JohnnyElectronic/EMF_Meters/10_LED_EMF_Meter_Replica/r1/img/10_LED_Lights2.jpg

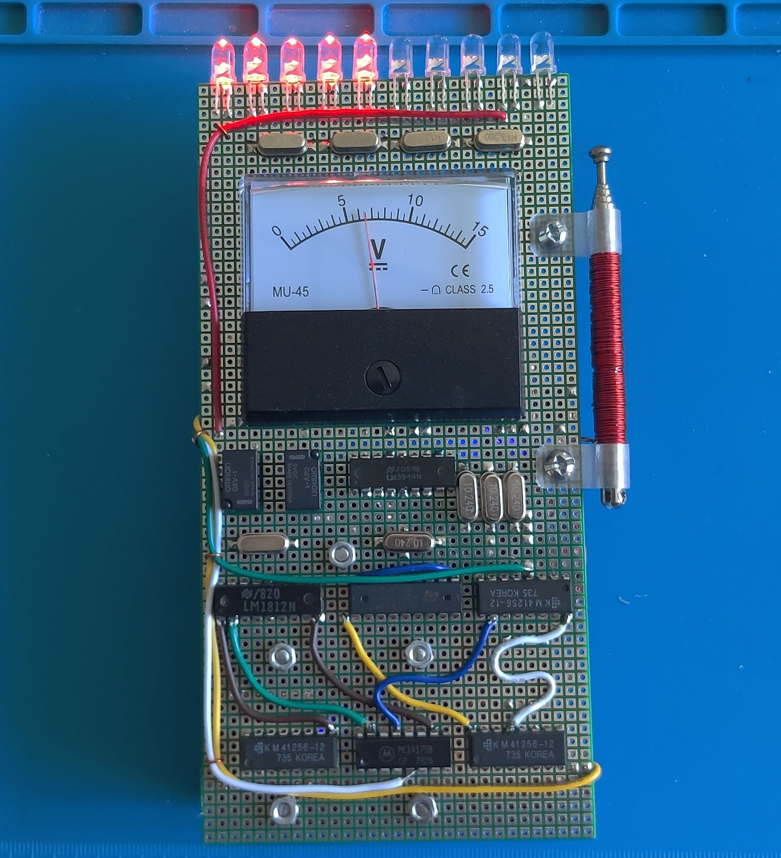
10_LED_EMF_Meter_Replica/r1/img/10_LED_Lights2.jpg
