JohnnyElectronic/EMF_Meters/EMF_Meter_Replica/r1/img/EMF_Meter_9v_buck_converted_b.jpg

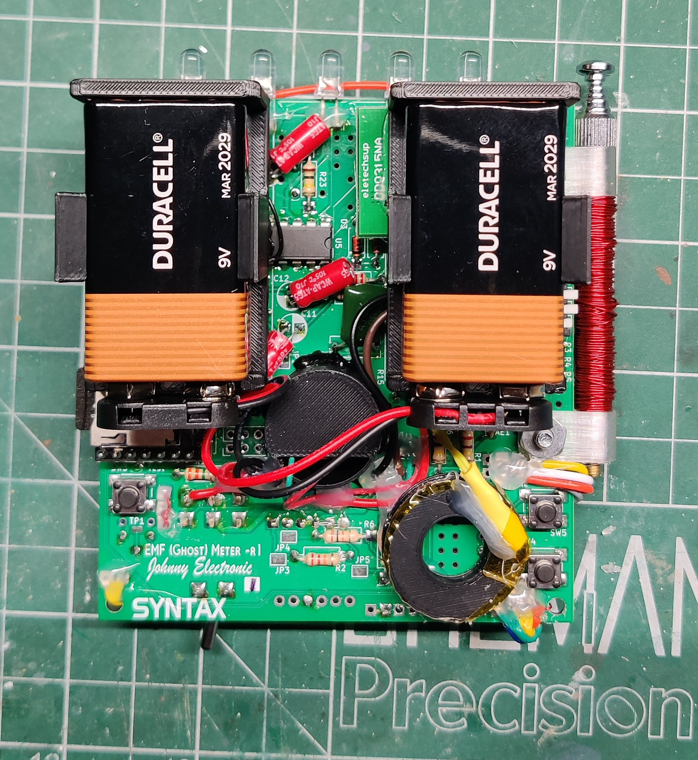
EMF_Meter_Replica/r1/img/EMF_Meter_9v_buck_converted_b.jpg
