JohnnyElectronic/EMF_Meters/EMF_Meter_Replica/r1/img/EMF_Meter_Label_0113_28x3.png

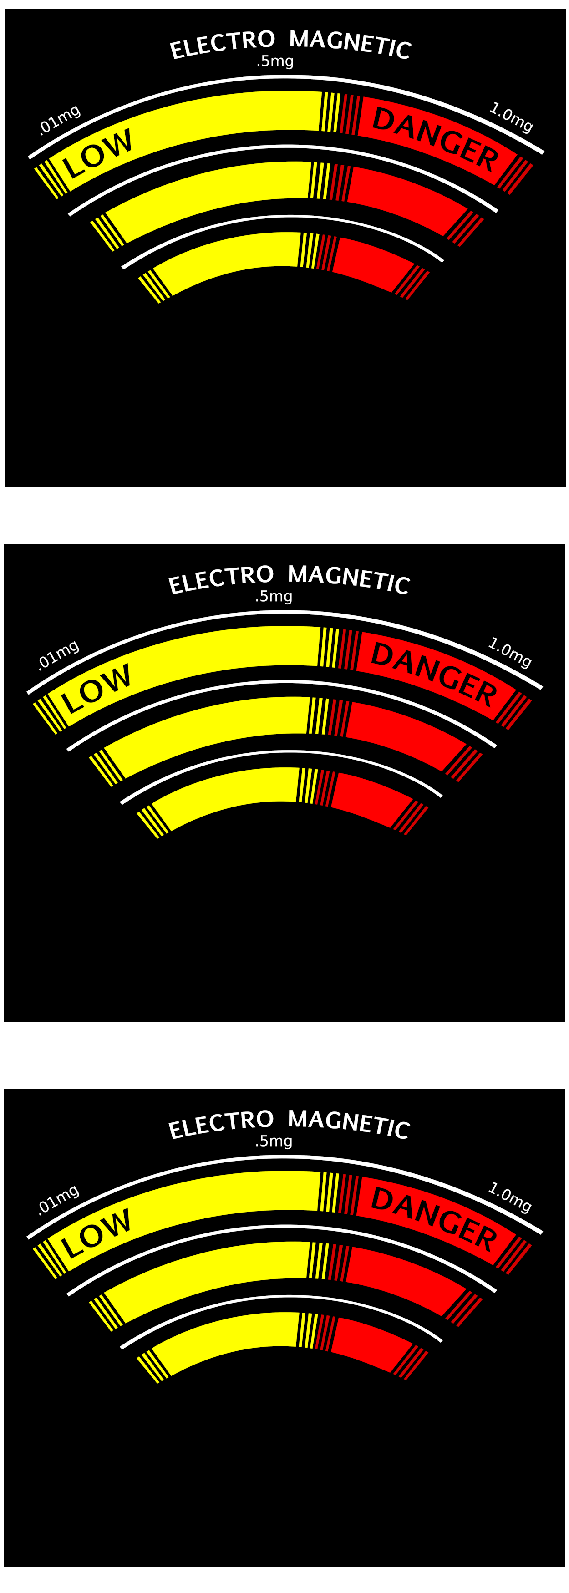
EMF_Meter_Replica/r1/img/EMF_Meter_Label_0113_28x3.png
