JohnnyElectronic/EMF_Meters/EMF_Meter_Replica/r2/img/EMF_6v_back.jpg

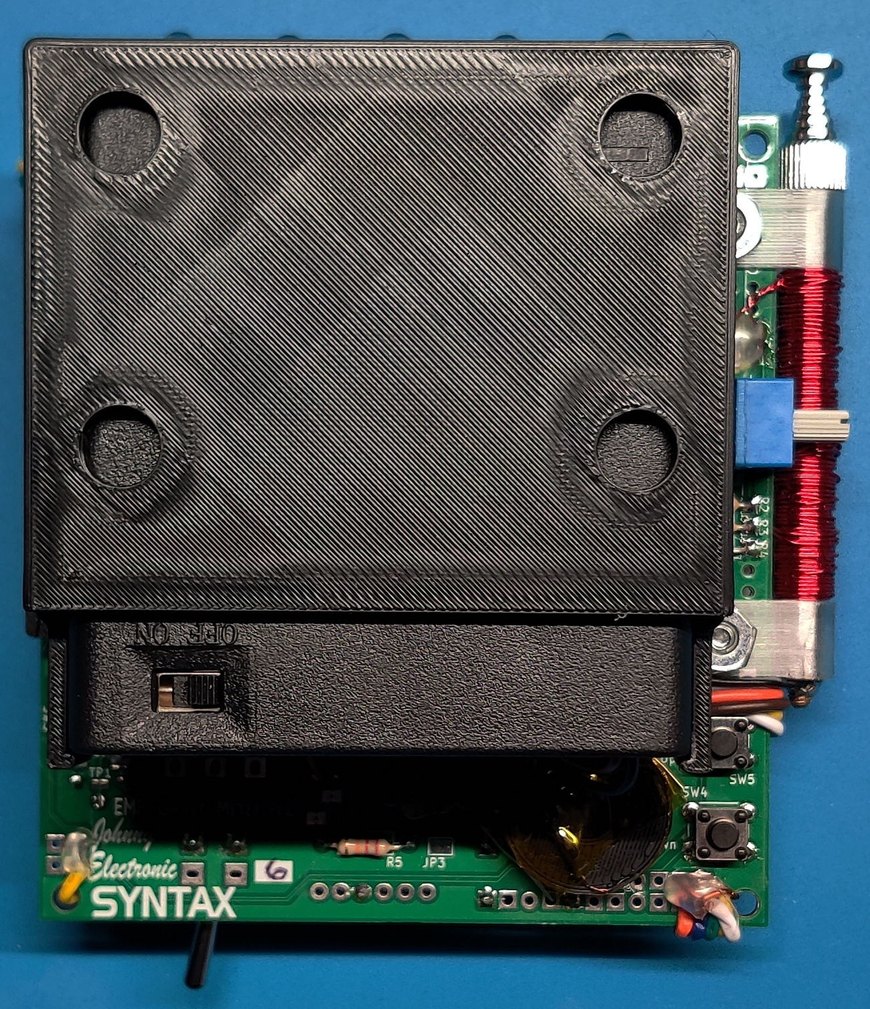
EMF_Meter_Replica/r2/img/EMF_6v_back.jpg
