JohnnyElectronic/EMF_Meters/EMF_Meter_Replica/r2/img/EMF_9v_front.jpg

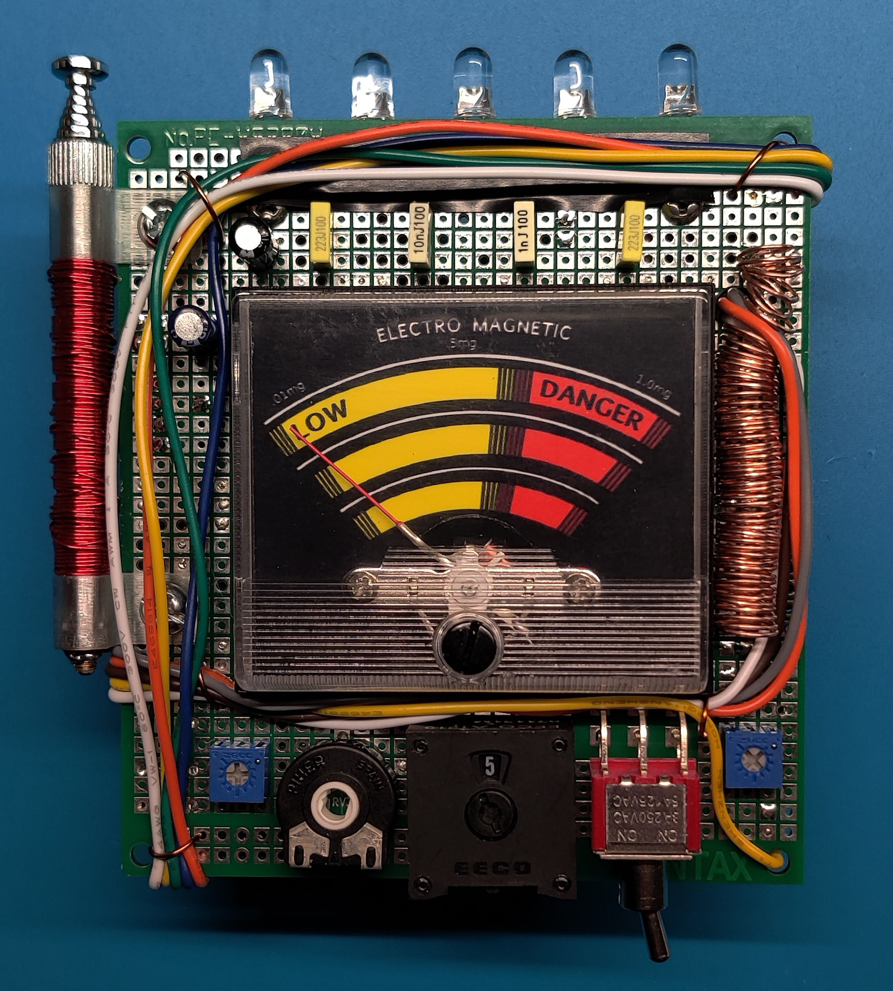
EMF_Meter_Replica/r2/img/EMF_9v_front.jpg
