JohnnyElectronic/EMF_Meters/10_LED_EMF_Meter_Replica/r2/doc/Top_Layout_Guide.pdf

t,6g*'

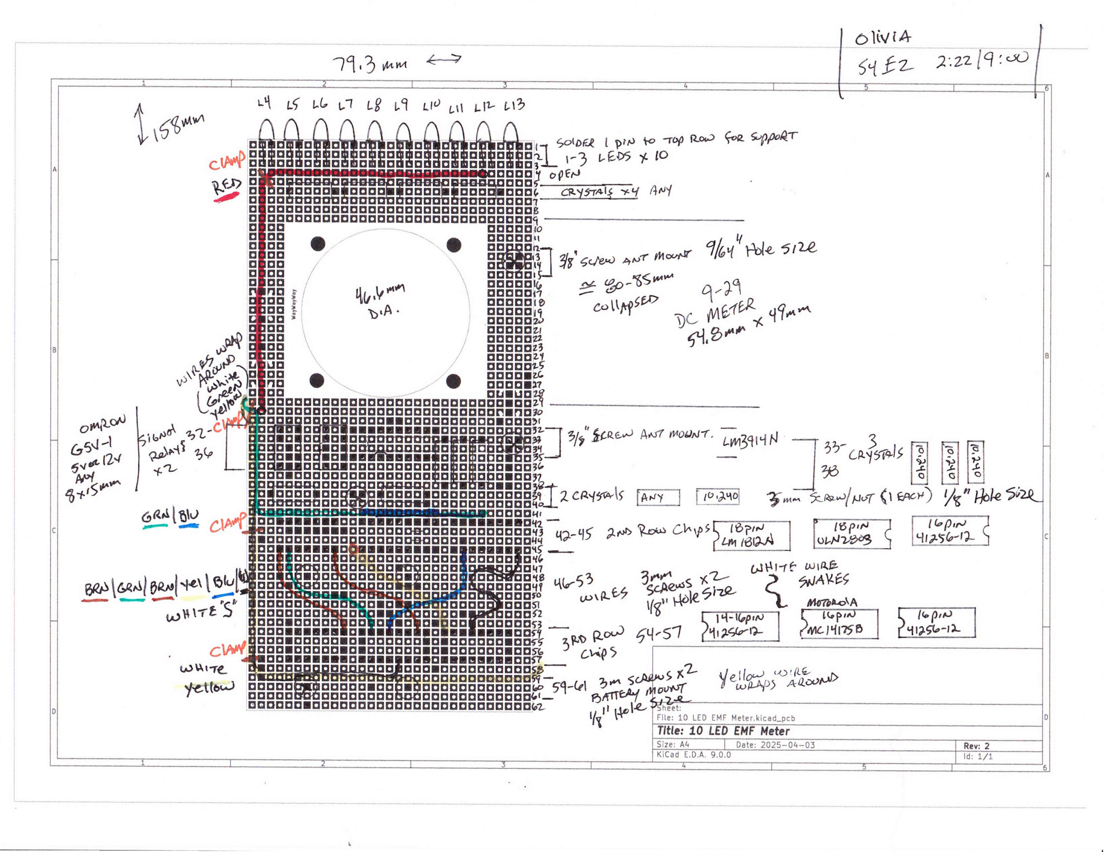
[picture p124: page 1]

'11,1 u- <'--' | ol(vl4 51tL 2"zz lq t'a

6aI[6tur .---

r"1 1ld ;rl LIL LtV
n QTDFJ I prp {. '-l t Lr>s | Qz opP"er lo 1oP fLa,2 )c lo o(Jl > | o0eP '-ffi*Vt | Apl

1r' s./* atn rhsqs ila"lt' r\>le 5 rLL

40.v"
b'A '

9t- to,g-XSVe
- oir1,1t* a']1 \L iua@*ql^^

4,bnn
"t't

or&d
?:::;r
fiTl*-

ll1ificto,,

A^r7 L'ouNa. tt5lrltl 150- ro?rds g )% | El' Tcag*ls tA^,y I t@ g^7**-w"rlp"r (ttxv) IEt Ifl L9 L9 ,/r, Lht"

6oAt*u]oj"l*'tB
purre

.9

cwrl,

,a-ts e,D?'bt 2n'rW,a61 ;W1 Vi-W,{l,

rrur7e

yatto'*) | ""# '1"1fr,f,!f*,,

5neetr
Fite:10 LED EMF Meter.kicad_pcb

te:2025-04-03

"rw
F*"; l"-
',l,,te'l t*:ii,*'* "I'x'itt" ' | L xasTutA ww*lw L\v5, 31fr*s ft'^ 'ff:'*w* -lpo eo., 5q'51 J | -.'^ | < | I cnp5
