JohnnyElectronic/EMF_Meters/10_LED_EMF_Meter_Replica/r1/doc/10_LED_EMF_Meter_Build_r1.1.pdf

# 10 LED EMF Meter Build

## Contents

## Description

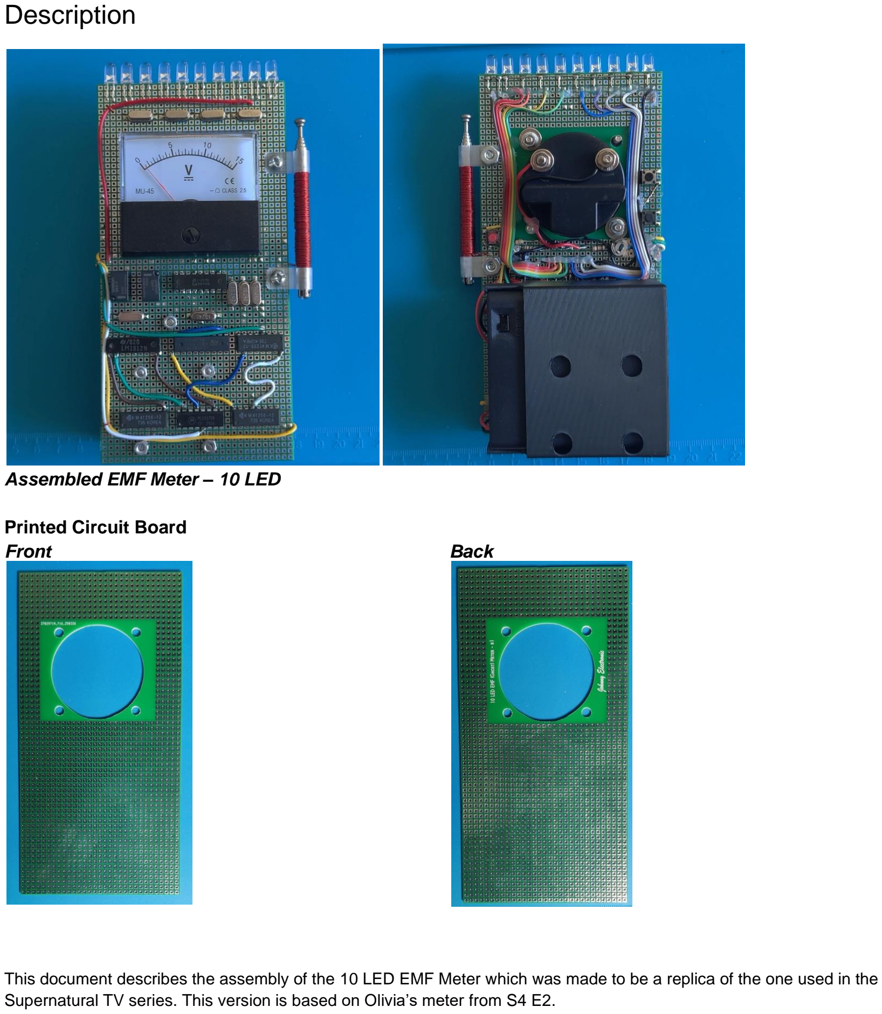
[picture p131: page 2]

Assembled EMF Meter – 10 LED

Printed Circuit Board
Front | Back

This document describes the assembly of the 10 LED EMF Meter which was made to be a replica of the one used in the Supernatural TV series. This version is based on Olivia’s meter from S4 E2.

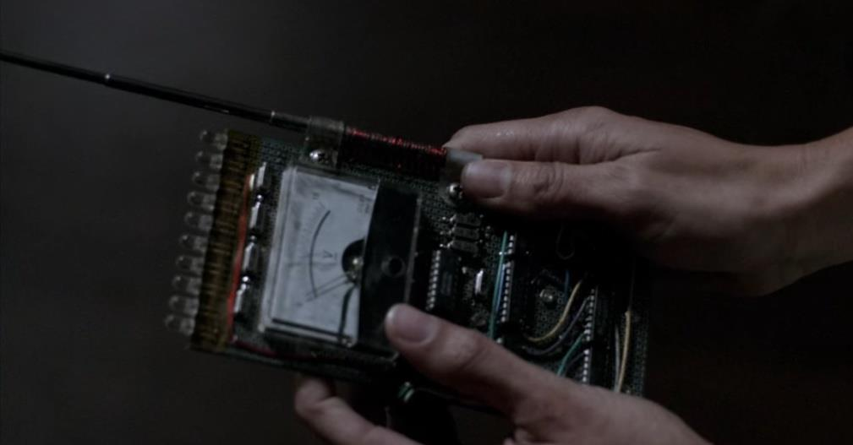
[picture p132: figure]

Olivia’s EMF Meter (S4 E2 2:22)

This is a prop only EMF meter and can manually create EMF events by pressing the program button or run a selection of pre-programmed sequences.

## Board Details

- PCB Dimensions: 79 mm x 158 mm
- 4 AA batteries to provide 6v with power
- Meter is a DC 0-15
- 10 LEDS in BAR mode
- 9 non-functional crystals
- LM3914 IC – functional
- 6 random IC’s, non-functional
- Right side mounted antenna, cosmetic
- 2 low voltage signal relays, non-functional

### Parts List

See the 10 LED EMF Board BOM for a detailed list of parts and part suppliers. A link to Github is provided in the references section at the end of this document.

## Pre-Assembled Boards

This board is currently hand built on perfboard using point to point solder connections. Thus pre-assembled boards will be very limited.

## Assembly Guide

Caution: Electrostatic discharge (ESD) is a sudden and momentary flow of electric current between two differently-charged objects when brought close together or when the dielectric between them breaks down, often creating a visible spark associated with the static electricity between the objects. ¹

1 Definition provided by From Wikipedia, the free encyclopedia. For more information on ESD see https://en.wikipedia.org/wiki/Electrostatic_discharge

This type of shock can cause damage to ESD sensitive parts such as those used in this build. Proper ESD protection and soldering equipment should be used to prevent damage to parts during assembly and implementation into your project.

Assembly Planning

This assembly uses all through hole parts except for possibly the 5-volt regulator. A medium to fine tip soldering iron is useful along with 0.034” or smaller flux core solder and extra flux if needed. See the references section for a YouTube video link on assembling this board.

### PCB Assembly

- PCB assembly can be completed in any order.
- This is a perfboard assembly and you will need to use the schematic for all the point to point connections. I’ve included a copy of my layout guide for functional and non-functional part placements.
- There is also an image of the board assembly with the battery pack removed so you can see a suggested layout.
- Since the battery supply is only 6v a LDO 5-volt regulator of at least 500ma will be needed to power the ATTiny85 and DFPlayer module.
- The position of the ATTiny85 should allow it to be removed easily for reprogramming. Suggest a socket be used.
- The position of the DFPlayer should allow easy access to the SD card. Also, the speaker will need to connect to this part and attach to the back of the battery holder or a different location.
- Hot glue any wire connections for added support.

### Antenna, Coil Assembly and Mounting

A coil of wire is wrapped around a telescopic antenna. I used 26 AWG red enameled wire to wrap around the antenna. Before wrapping the antenna with wire, you will want to attach the p-clips with 6-32 3/8” screws with nuts. You will need to drill holes into the PCB for the antenna to be mounted. Then align the P-clips to the hole positions but do not mount it to the board. Once you have the p-clips aligned tighten the nuts so the clips do not move. You can now start wrapping the enameled wire between the two p-clips. You can start/end the wrap from either end.
- Make the first layer wrap tight and uniform around the antenna. On the second pass feel free to add multiple layers and give it a non-uniform look much like a free-handed wire wrap.
- Mount the antenna/coil using P-Clips. 3D files are also available for printing these.
- You can solder the wire ends to one of the perfboard pads to make it look functional.

### Attach Speaker

- Connect the speaker to pins 6 & 8 of the DFPlayer module. I suggest the speaker be hot glued to the back of the battery pack holder but you may see other options.

### Mounting Battery Pack

- Use the AA battery pack holder as a drilling template to drill 4 holes into the PCB for mounting. Look at the reference layout for proper positioning.
- Using hot glue attach the speaker to the bottom of the battery pack holder. Make sure you have enough wire to allow the battery pack to attach to the PCB.
- Use either 4-40 or M3 screws to mount the battery pack holder with a minimum of 8-10mm standoffs. I’ve provided some 3D files a 4-AA battery pack holder so they can be mounted to this board.

### Mounting Meter

- The DC meter is mounted in the cutouts/holes provided in the PCB.
- Connect the meter wires noting the proper polarity.

### Adding Cosmetic Wires

- The available images for this meter are limited. I’ve made some guesses as to wiring for the meter front. All wires are non-functional except for the top red wire so placement is at the builder’s discretion. The top RED wire was used to provide LED + power. See “Assembly Images” for suggested wire routes.

## Sound Files (MP3)

The sound files are stored in a folder named /mp3 on the SD card. Six files are available but only five are used in the program for the EMF meter. This table lists the files, functionality, and associated code define. The sound files are available in Github (The same files are used for the EMF Meter Build and they are available from that folder under /mp3). The link is in the references section at the end of this document.

File Name | Define Name | Function
0001_emf start.mp3 | EMF_TONE_START | Initial start up when a signal is detected or test button pressed
0002_emf low short.mp3 | EMF_TONE_LOW | Used for mid-point signals that are neither high or low
0003_emf steady short.mp3 | EMF_TONE_STEADY | Not used
0004_emf steady long.mp3 | EMF_TONE_STEADYL | High tone when signal reaches maximum
0005_emf steady end.mp3 | EMF_TONE_END | Signal going back down to off
0006_emf power up.mp3 | EMF_POWER_UP | Used for initial setup/power on.

## EMF Meter Adjustments and Power Up

1. Before powering up the meter check for any shorts by doing an ohm measurement across the +/-battery connector.
2. Adjust the meter potentiometer to the midpoint.
3. Insert SD card with audio files in to the DFPlayer.
4. Install the AA batteries and flip the power pack switch on.
5. With in a second you should see the meter briefly deflect and a sound from the DFPlayer.
6. Press and hold the Test/Program Button and you should see the LEDS and VU Meter deflect and some sound effects. While keeping the button pressed adjust the meter potentiometer until all 10 LEDS are on.
7. Using a long button press you can manually make EMF events.
8. A quick button press will cycle through the pre-programmed EMF event sequences. An LED will light when a programmed sequence is running.
9. While pressing the Test/Program button check that the Volume Up/Down buttons are functional.
10. Removing the AA battery pack from the holder is easiest by gently pulling the locking tabs away from the battery pack and shaking the meter a few times to let gravity release the battery back. You should now be able to slide the pack out completely.

## Assembly Images

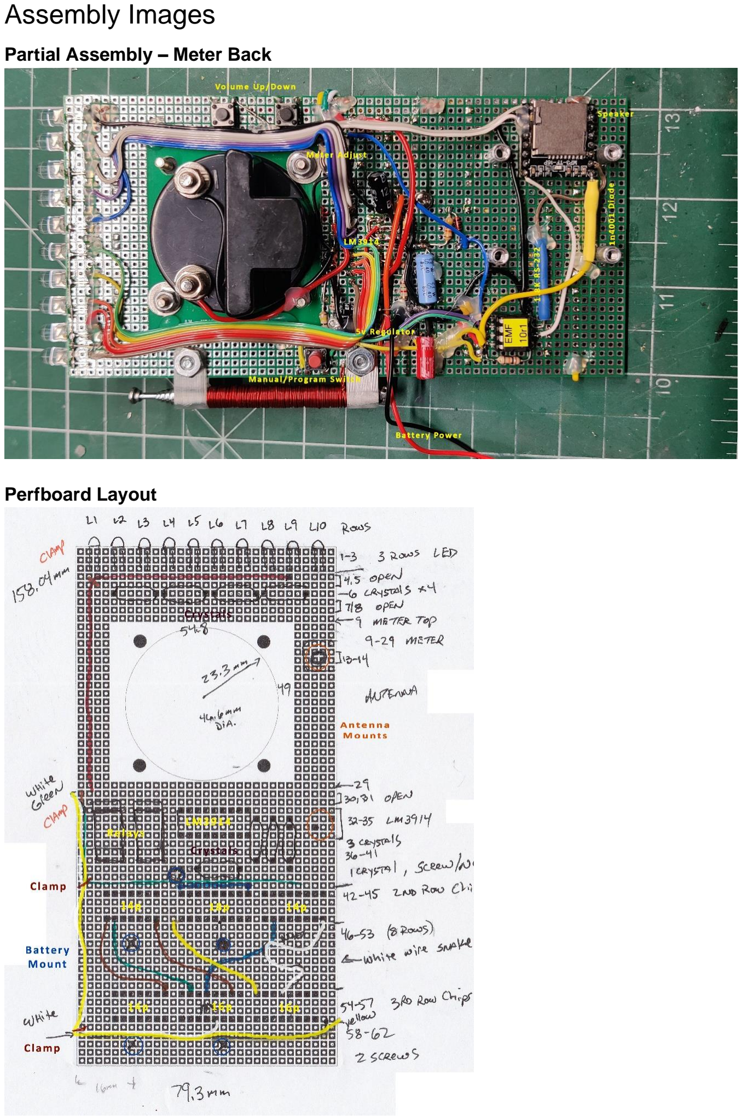
[picture p133: page 6]

Partial Assembly – Meter Back

Perfboard Layout

## References

- Github: Development board documentation, schematics, and related files.
- https://github.com/JohnnyElectronic/EMF_Meters/
- YouTube: Board assembly and project videos that are related to this project.
- https://www.youtube.com/@Johnny_Electronic

## Revisions

R1.1 First board release, First document release

Disclaimer

This information is provided “as-is” with no representation or warranty of any kind whether express or implied. However, I’ve tried to make this document (as well as the supporting videos) as useful and accurate as possible. If you find something that is incorrect or confusing, please let me know as I would like to make the correction so others will not have the same issue.

This meter is for entertainment purposes only and there is no representation as to the accuracy of the meter readings.

Feel free to email me any time for issues you may have with this build.
johnnyelectronic1@gmail.com

Legal note

Microchip, AVR, tinyAVR, megaAVR, ICSP, In-Circuit Serial Programming, are names of Microchip, it’s products and product lines, and as such are all trademarks of Microchip.
