JohnnyElectronic/EMF_Meters/EMF_Meter_Replica/r1/img/Partial_Assembly2.jpg

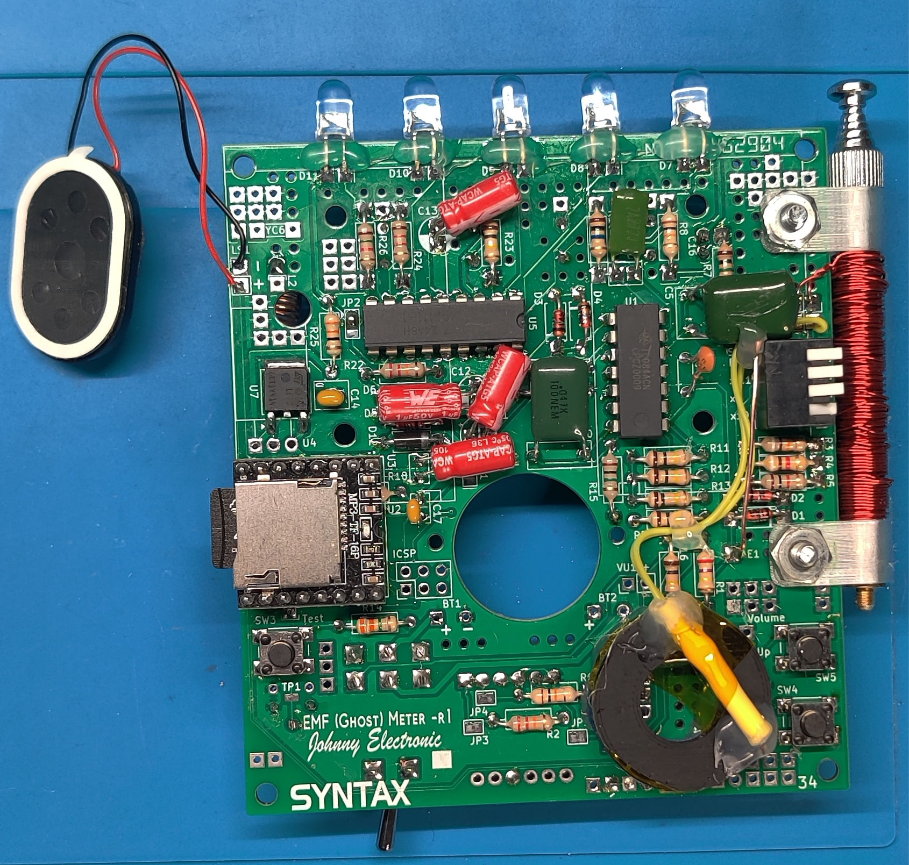
EMF_Meter_Replica/r1/img/Partial_Assembly2.jpg
