JohnnyElectronic/EMF_Meters/EMF_Meter_Replica/Journal/EMF Meter Journal Page_br_tn.jpg

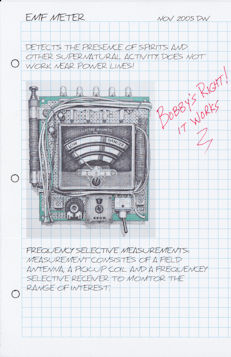
EMF_Meter_Replica/Journal/EMF Meter Journal Page_br_tn.jpg
