JohnnyElectronic/EMF_Meters/EMF_Meter_Replica/Journal/EMF Meter Journal Page_left_cs_tn.jpg

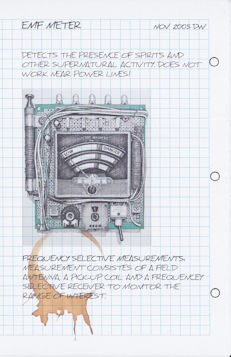
EMF_Meter_Replica/Journal/EMF Meter Journal Page_left_cs_tn.jpg
