JohnnyElectronic/EMF_Meters/EMF_Meter_Replica/r2/schematics/EMF_Meter_r2.pdf

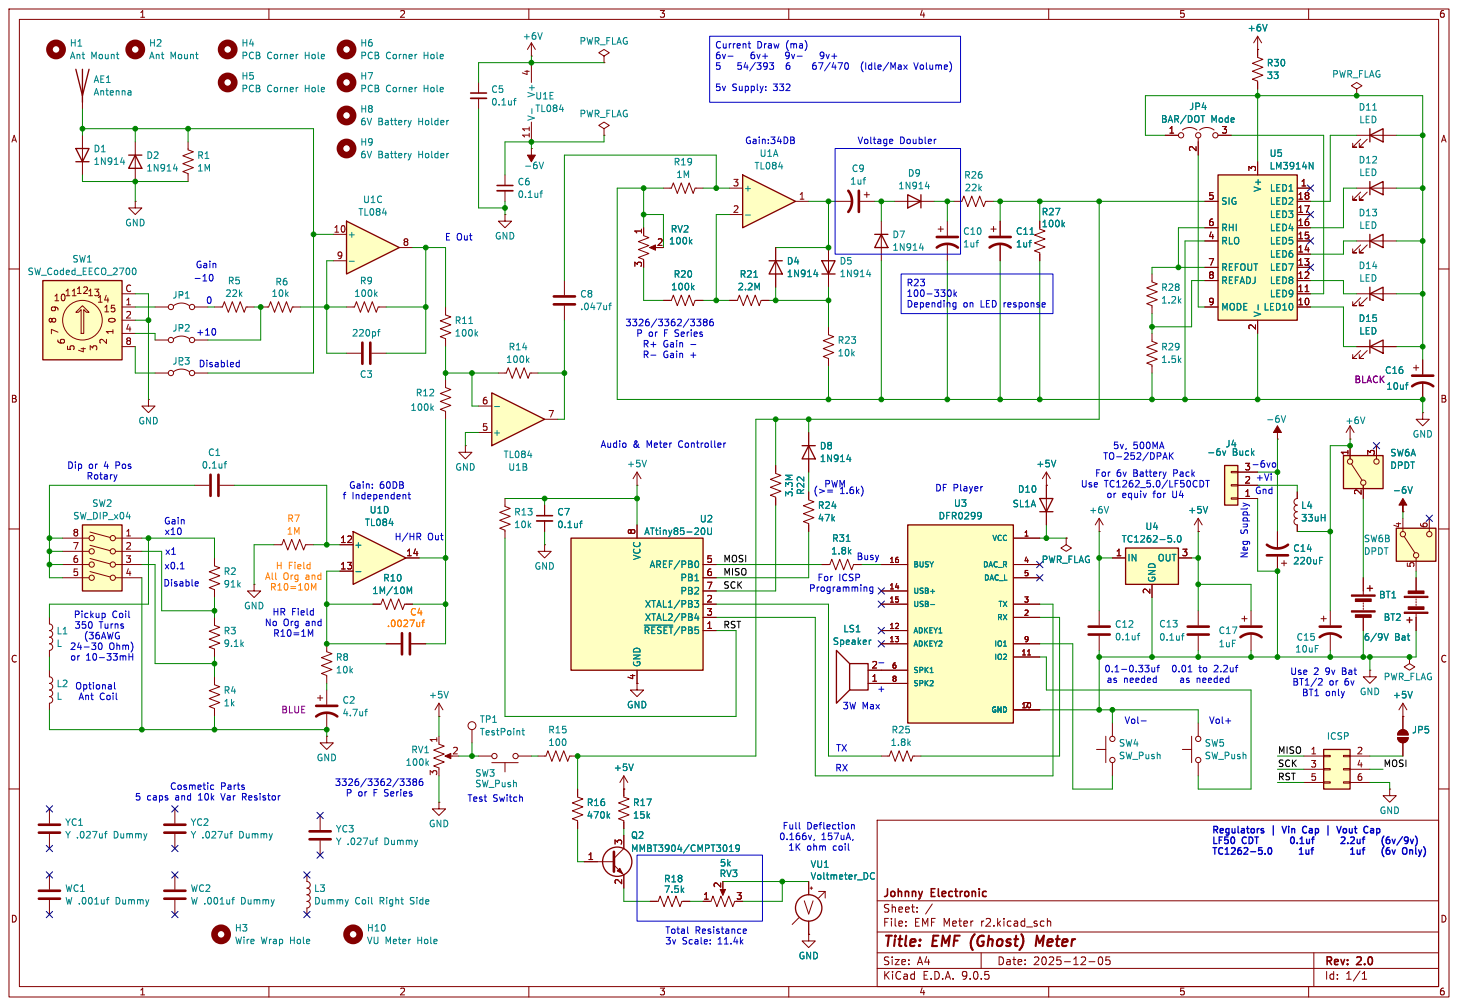
[picture p160: page 1]

6V Battery Holder H6PCB Corner Hole R11

JP1~ YC2 Y .027uf Dummy WC2 W .001uf Dummy H3 Wire Wrap Hole

3326/3362/3386 P or F Series R+ Gain - R- Gain +

TO-252/DPAK HR Field No Org and R10=1M

or equiv for U4 H Field All Org and R10=10M
