JohnnyElectronic/EMF_Meters/10_LED_EMF_Meter_Replica/r2/schematics/10_LED_EMF_Meter_r2.pdf

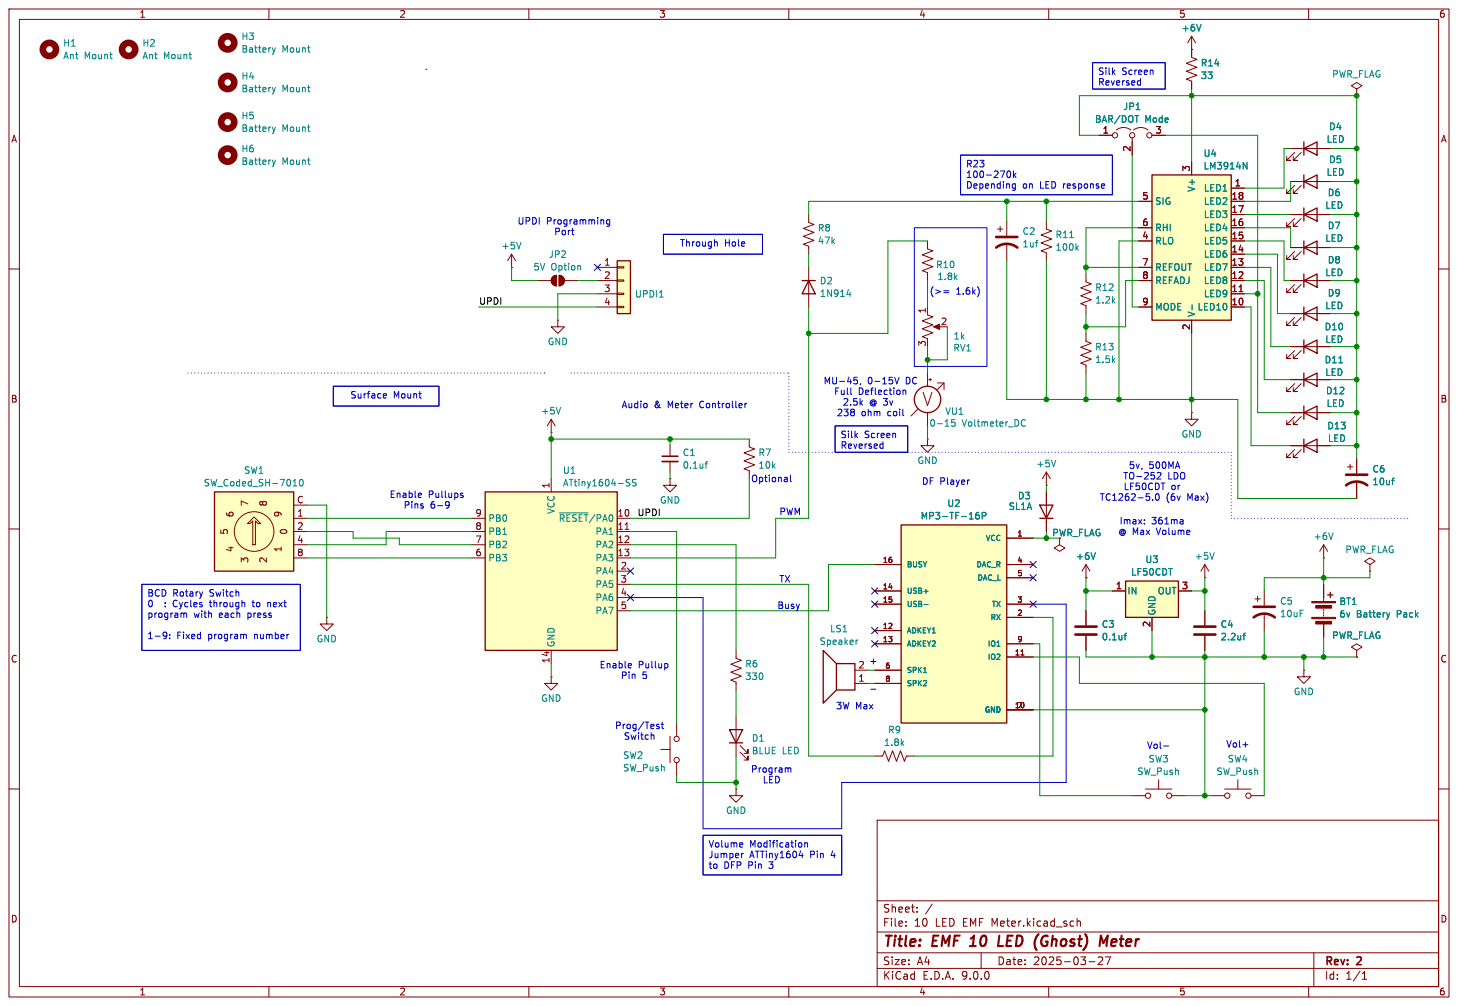
[picture p161: page 1]

LED GND
2.5k @ 3v 238 ohm coil 3W Max Busy

100-270k Depending on LED response

Imax: 361ma @ Max Volume Prog/Test Switch
