JohnnyElectronic/EMF_Meters/EMF_Meter_Replica/r1/schematics/EMF_Meter_r1.1.pdf

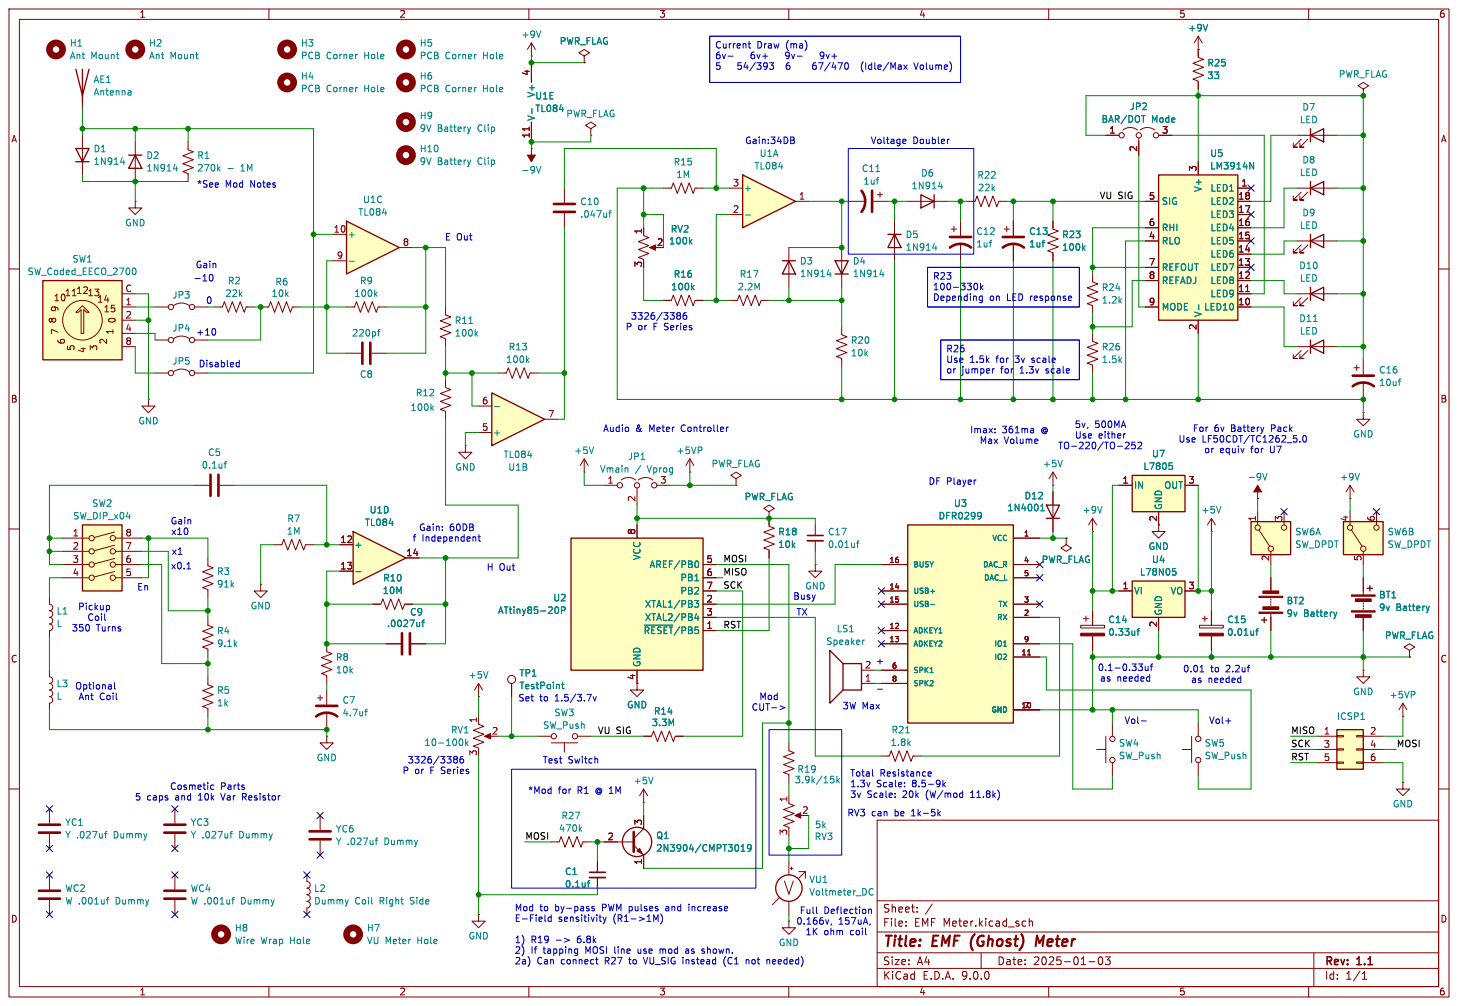
[picture p162: page 1]

H4PCB Corner Hole H3PCB Corner Hole +
9V Battery Clip H10

9V Battery Clip H5PCB Corner Hole H6PCB Corner Hole

or jumper for 1.3v scale R23

5v, 500MA Use either TO-220/TO-252

YC6 Y .027uf Dummy L2Dummy Coil Right Side GND
