JohnnyElectronic/EMF_Meters/10_LED_EMF_Meter_Replica/r1/schematics/10_LED_EMF_Meter.pdf

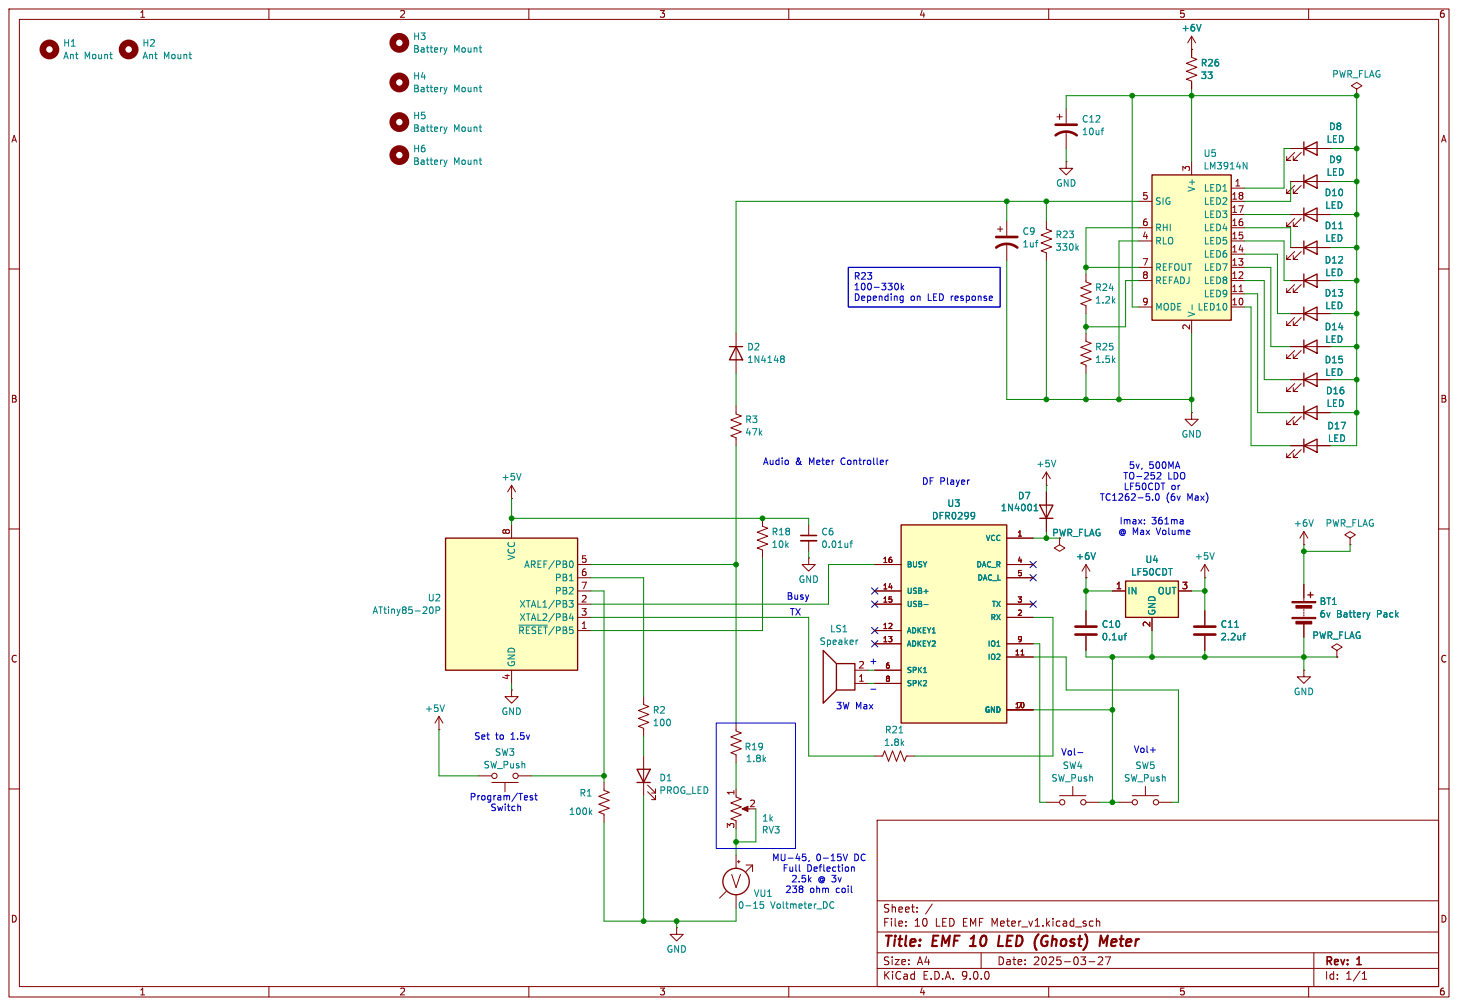
[picture p163: page 1]

100-330k Depending on LED response
