JohnnyElectronic/EMF_Meters/EMF_Meter_Replica/3D/EMF_Meter_Base_r2.pdf

2

1

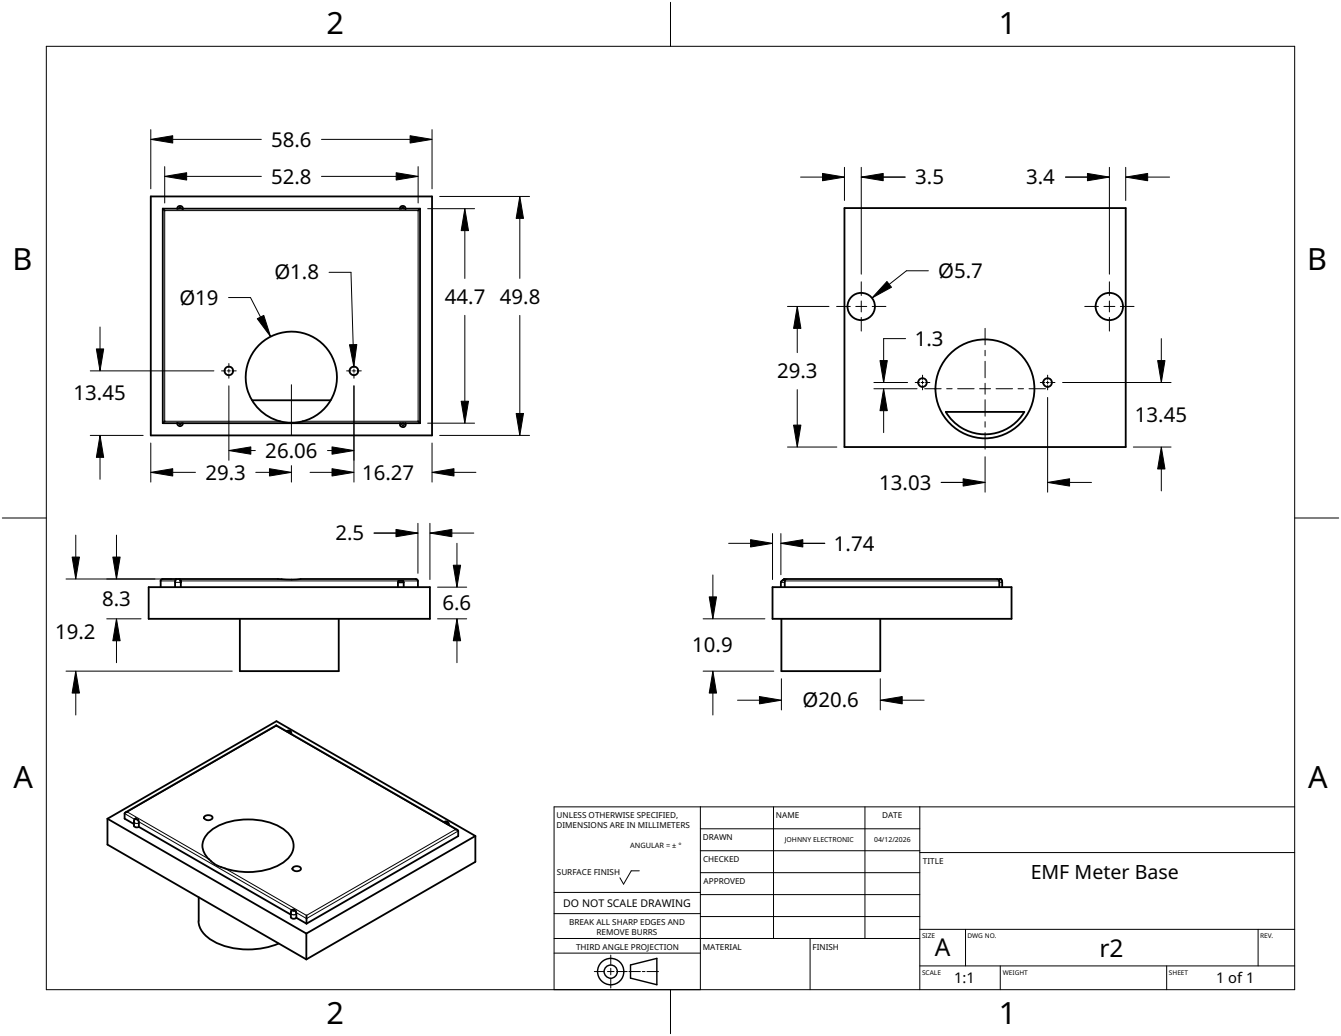
[picture p164: page 1]
MATERIAL; FINISH

UNLESS OTHERWISE SPECIFIED, DIMENSIONS ARE IN MILLIMETERS ANGULAR = ± ° SURFACE FINISH | | NAME | DATE

DRAWN | JOHNNY ELECTRONIC | 04/12/2026

CHECKED | | | TITLE EMF Meter Base

APPROVED

DO NOT SCALE DRAWING
BREAK ALL SHARP EDGES AND
REMOVE BURRS
THIRD ANGLE PROJECTION

SIZE A | DWG NO. r2 | REV.

SCALE 1:1 | WEIGHT | SHEET 1 of 1
