JohnnyElectronic/EMF_Meters/EMF_Meter_Replica/3D/9v_Battery_Holder.pdf

2
1

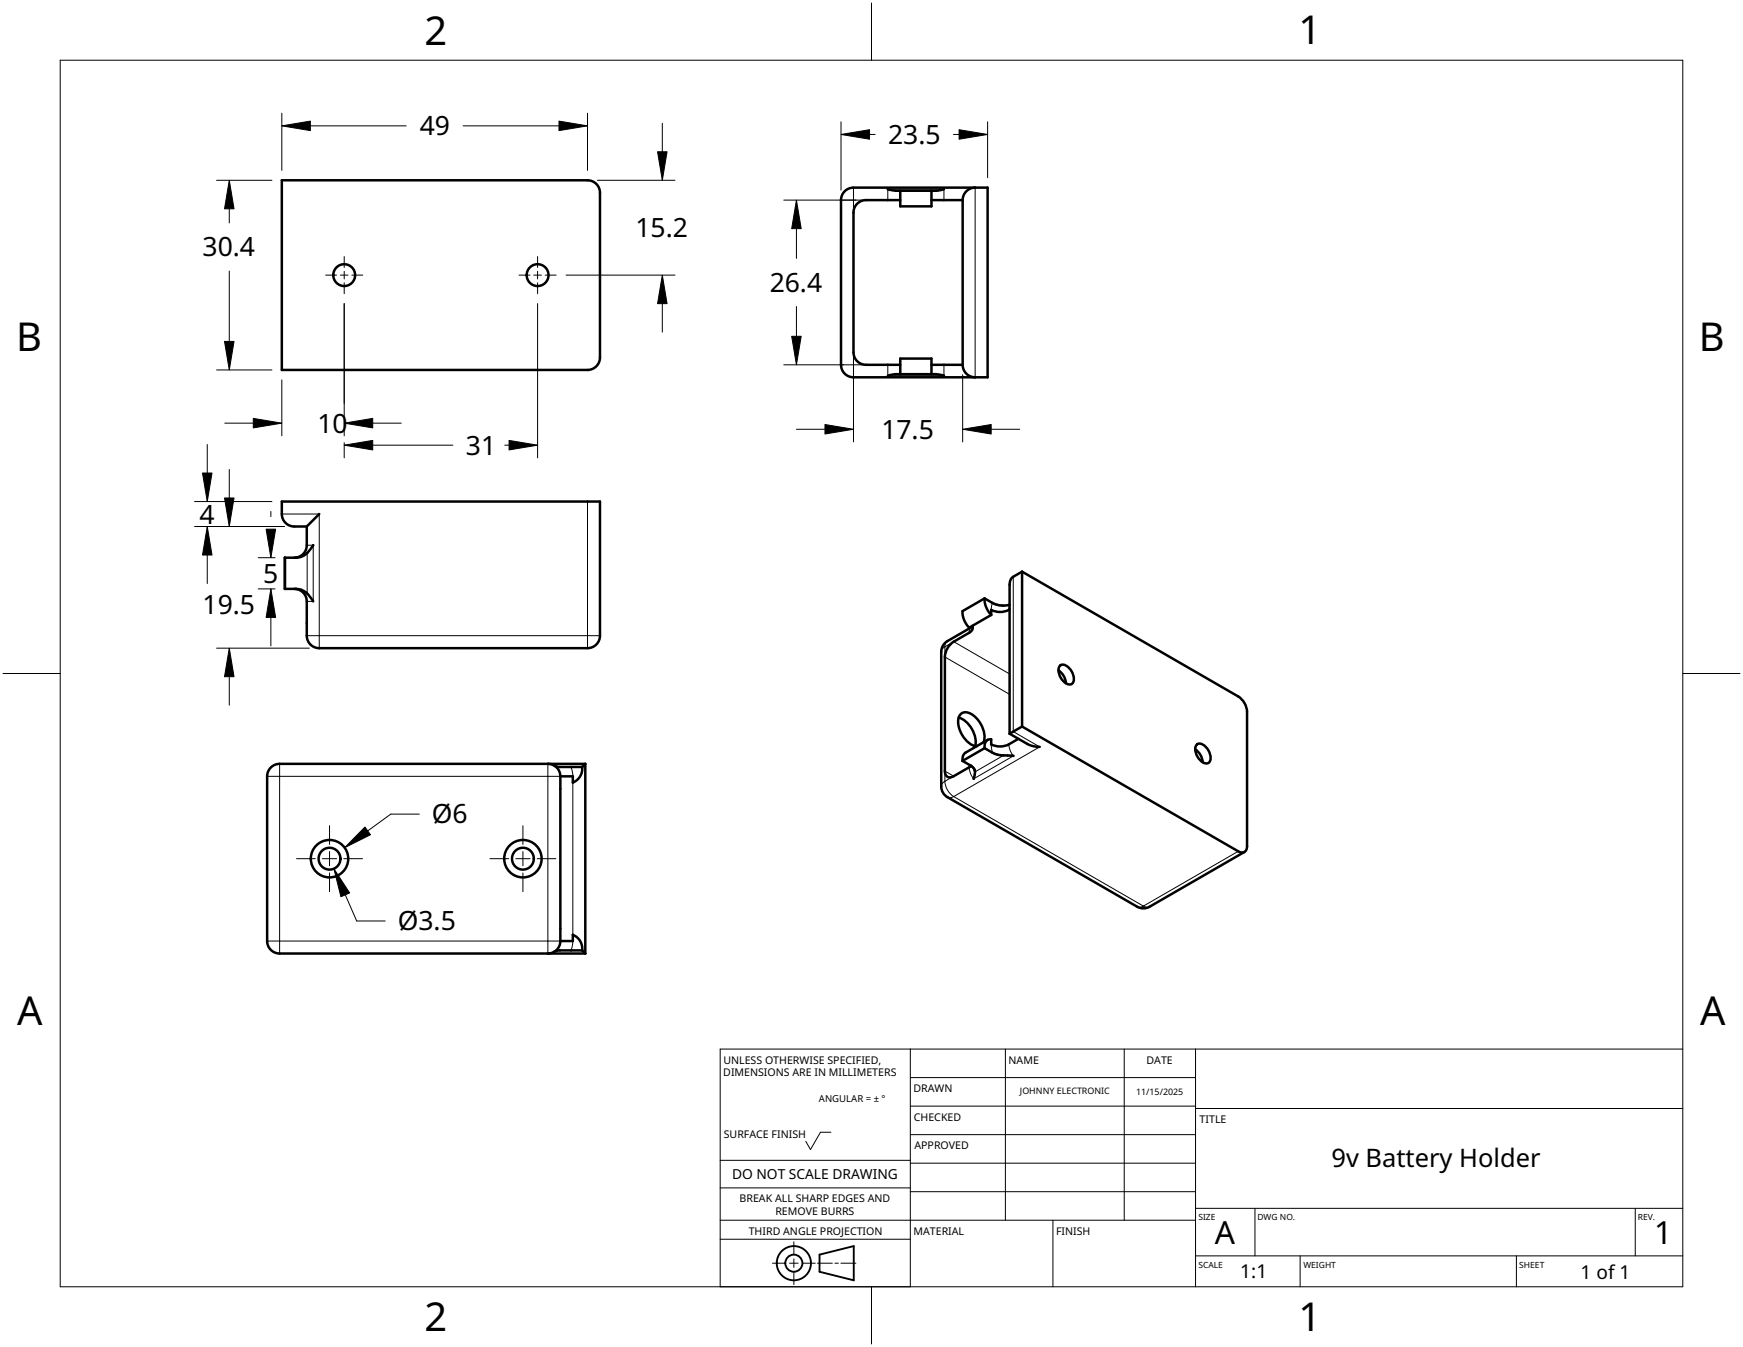
[picture p165: page 1]
MATERIAL; FINISH

UNLESS OTHERWISE SPECIFIED, DIMENSIONS ARE IN MILLIMETERS ANGULAR = ± ° SURFACE FINISH | | NAME | DATE

DRAWN | JOHNNY ELECTRONIC | 11/15/2025

CHECKED | | | TITLE 9v Battery Holder

APPROVED

DO NOT SCALE DRAWING

BREAK ALL SHARP EDGES AND

REMOVE BURRS
THIRD ANGLE PROJECTION

SIZE A | DWG NO. | REV. 1

SCALE 1:1 | WEIGHT | SHEET 1 of 1
