JohnnyElectronic/EMF_Meters/EMF_Meter_Replica/3D/AA_Bat_EMF_r2_Drawing.pdf

2

1

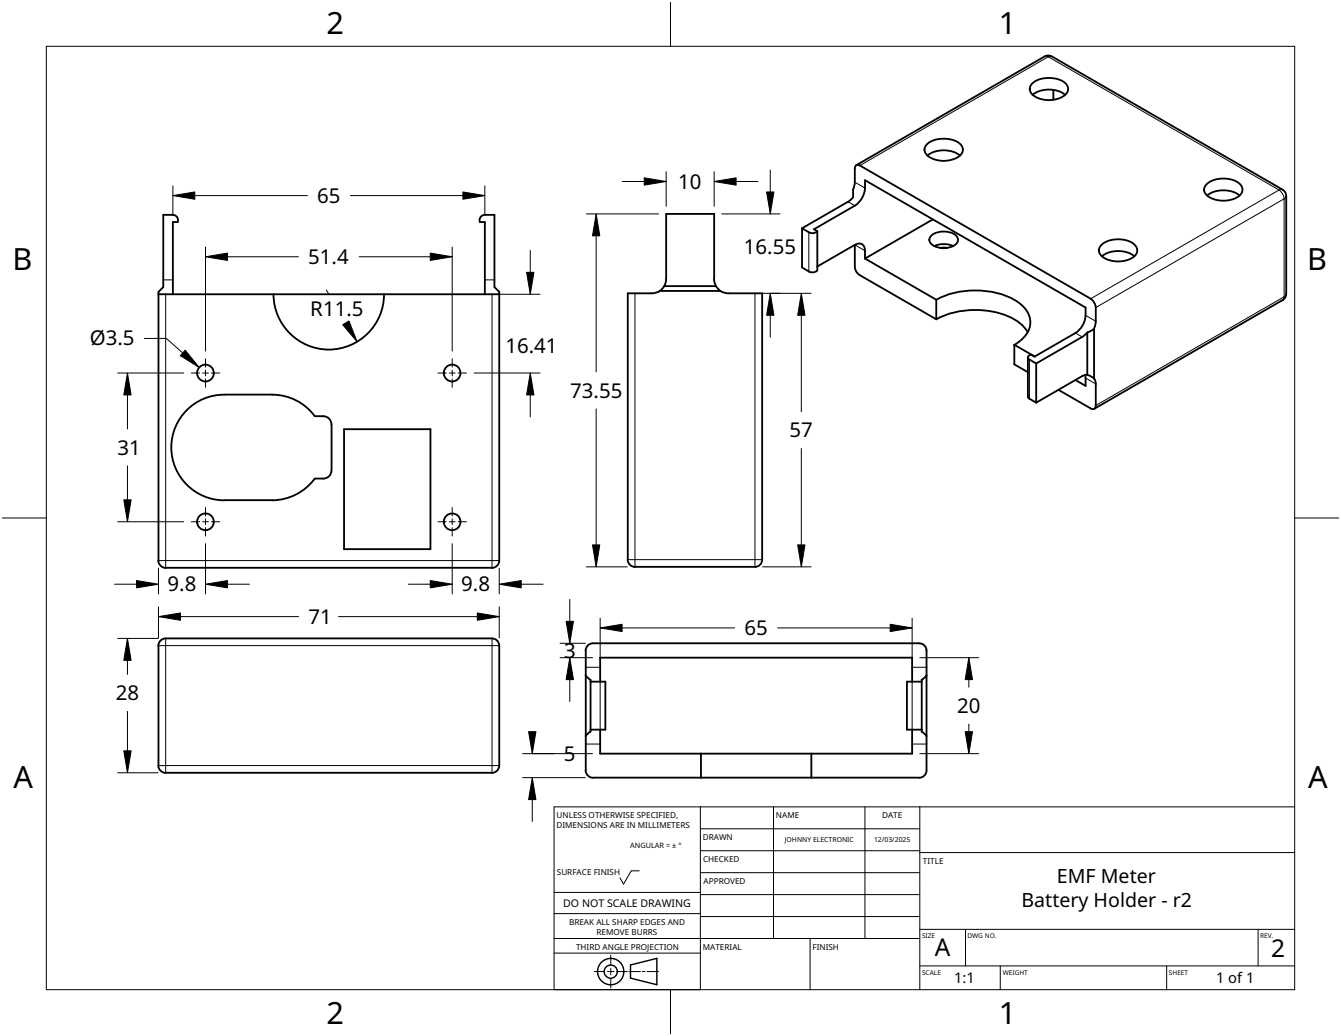
[picture p166: page 1]
MATERIAL; FINISH

UNLESS OTHERWISE SPECIFIED, DIMENSIONS ARE IN MILLIMETERS ANGULAR = ± ° SURFACE FINISH | | NAME | DATE

DRAWN | JOHNNY ELECTRONIC | 12/03/2025

CHECKED | | | TITLE EMF Meter Battery Holder - r2

APPROVED

DO NOT SCALE DRAWING
BREAK ALL SHARP EDGES AND
REMOVE BURRS
THIRD ANGLE PROJECTION

SIZE A | DWG NO. | REV. 2

SCALE 1:1 | WEIGHT | SHEET 1 of 1
