JohnnyElectronic/EMF_Meters/EMF_Meter_Replica/3D/AA_Battery_Pack_Holder_EMF.pdf

2
1

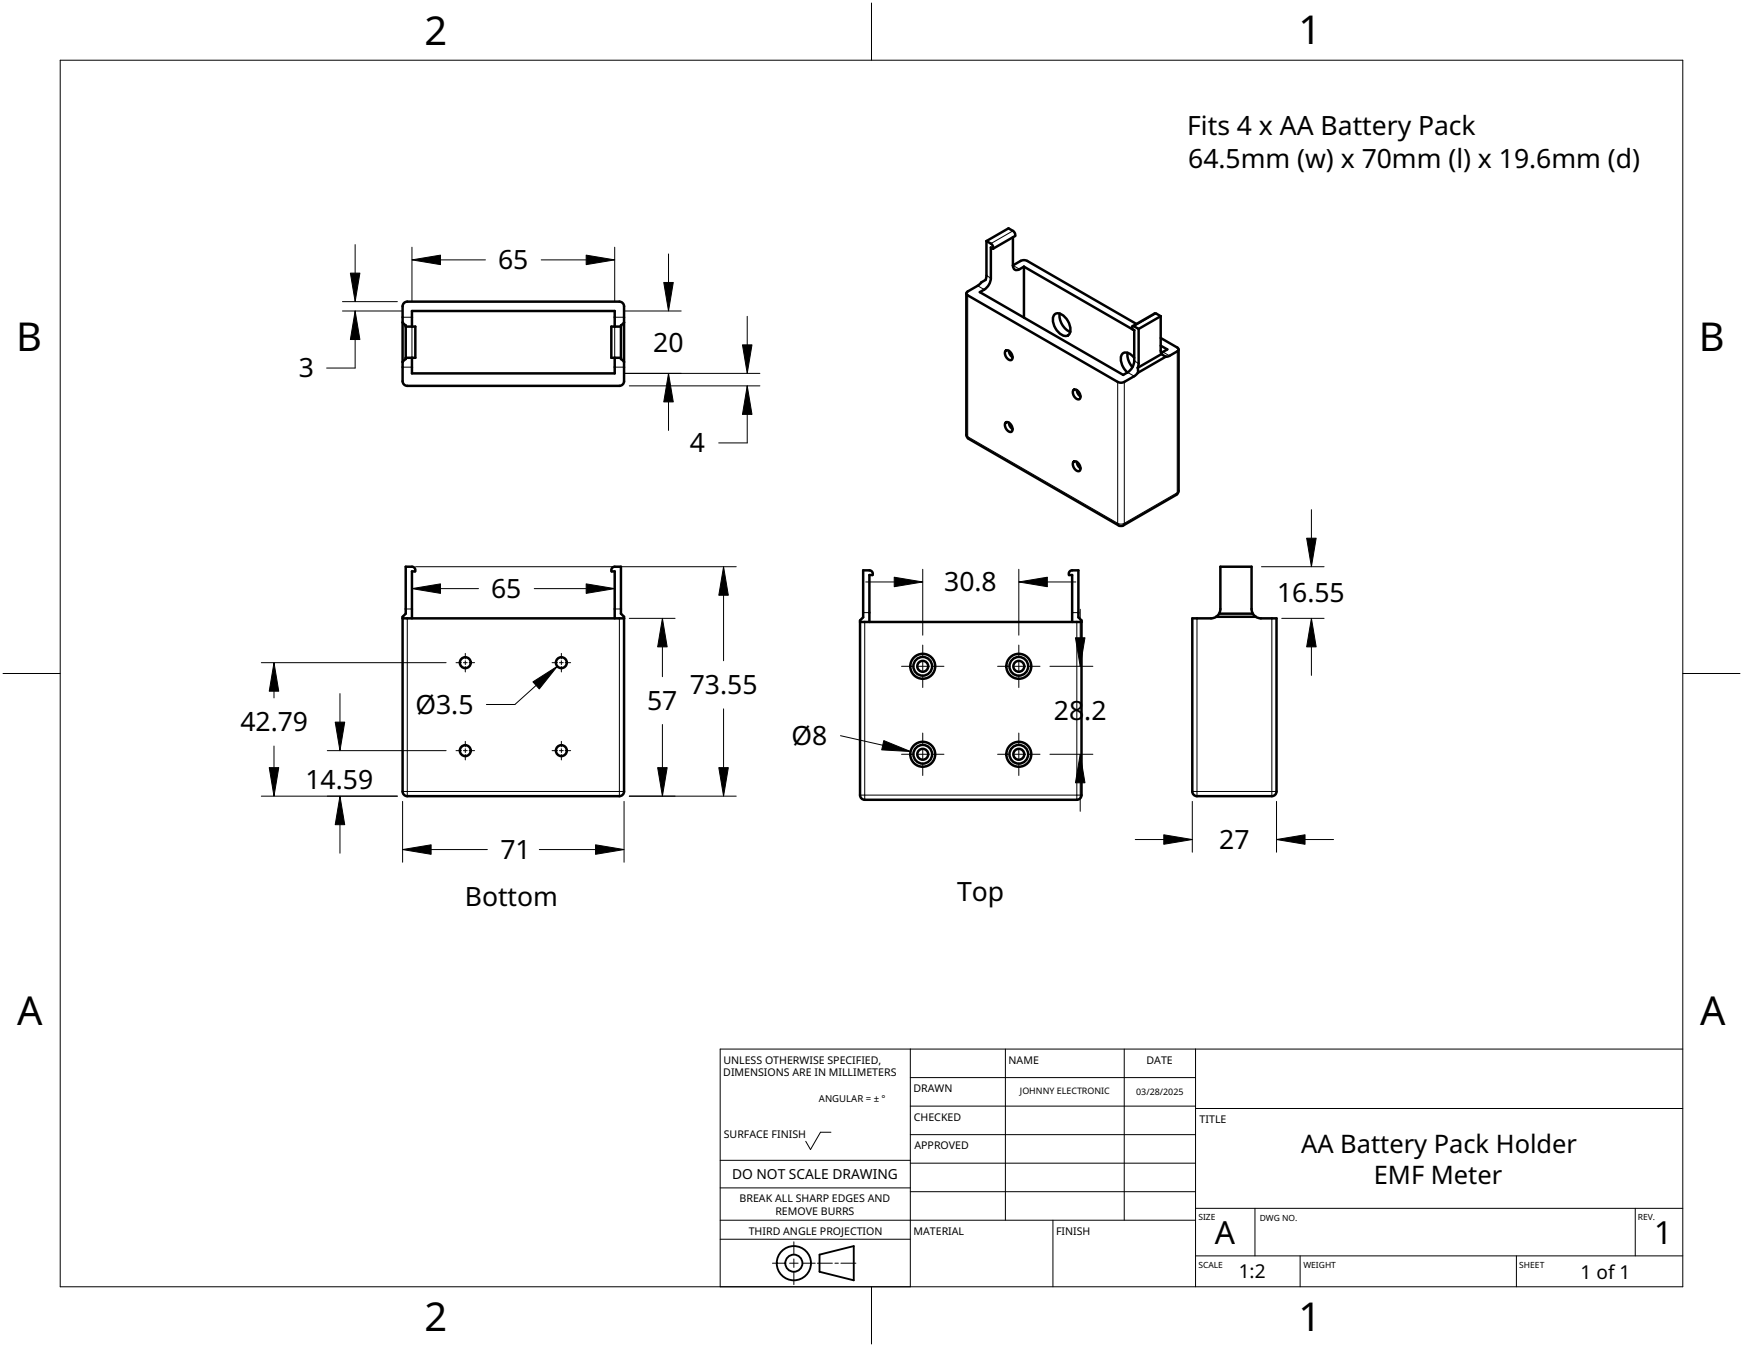
[picture p167: page 1]
MATERIAL; FINISH; Bottom; Top

Fits 4 x AA Battery Pack

UNLESS OTHERWISE SPECIFIED, DIMENSIONS ARE IN MILLIMETERS ANGULAR = ± ° SURFACE FINISH | | NAME | DATE

DRAWN | JOHNNY ELECTRONIC | 03/28/2025

CHECKED | | | TITLE AA Battery Pack Holder EMF Meter

APPROVED

DO NOT SCALE DRAWING

BREAK ALL SHARP EDGES AND

REMOVE BURRS
THIRD ANGLE PROJECTION

SIZE A | DWG NO. | REV. 1

SCALE 1:2 | WEIGHT | SHEET 1 of 1
