JohnnyElectronic/EMF_Meters/EMF_Meter_Replica/3D/EMF_Meter_Base_r1.pdf

2
1

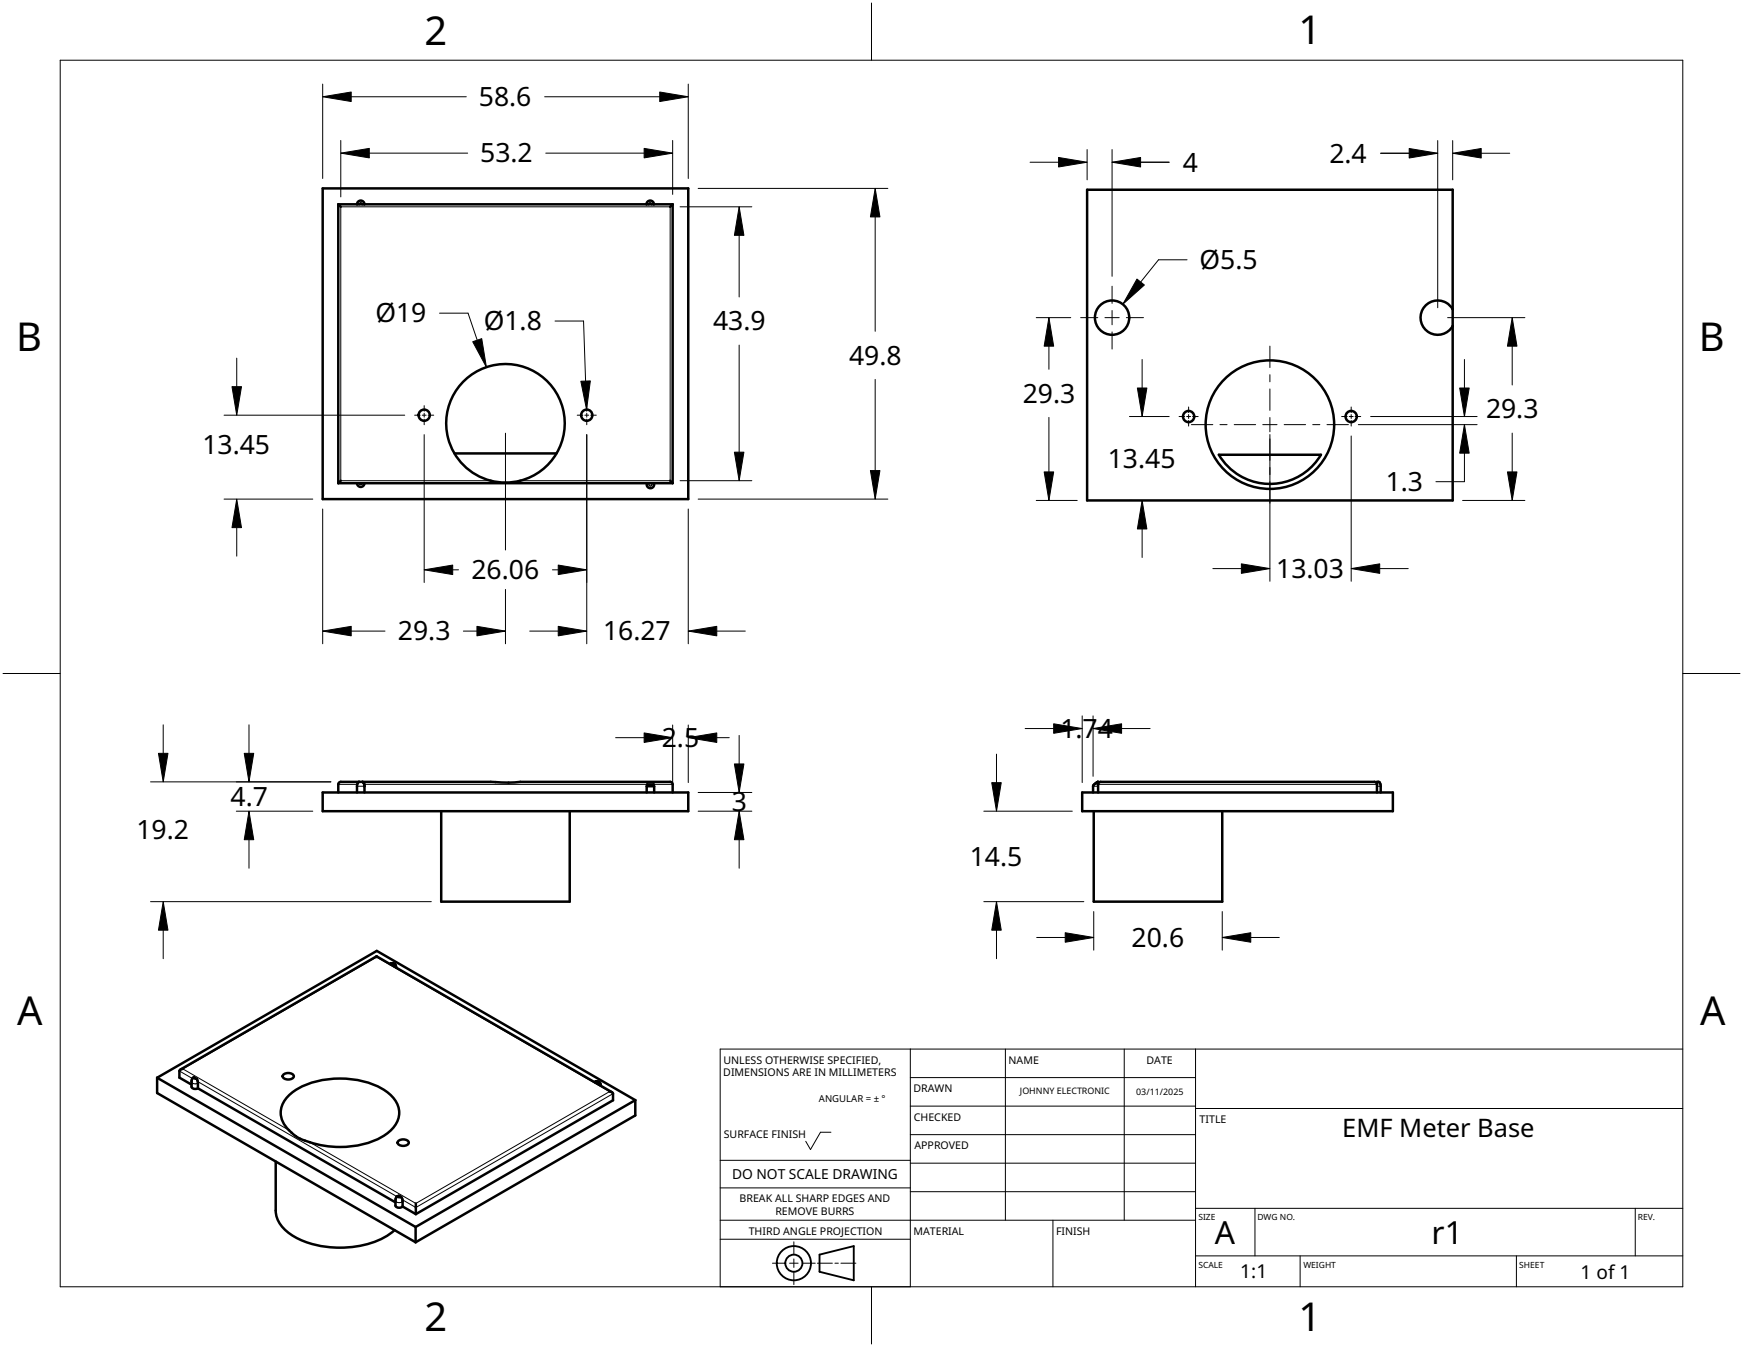
[picture p168: page 1]
MATERIAL; FINISH

UNLESS OTHERWISE SPECIFIED, DIMENSIONS ARE IN MILLIMETERS ANGULAR = ± ° SURFACE FINISH | | NAME | DATE

DRAWN | JOHNNY ELECTRONIC | 03/11/2025

CHECKED | | | TITLE EMF Meter Base

APPROVED

DO NOT SCALE DRAWING

BREAK ALL SHARP EDGES AND

REMOVE BURRS
THIRD ANGLE PROJECTION

SIZE A | DWG NO. r1 | REV.

SCALE 1:1 | WEIGHT | SHEET 1 of 1
