JohnnyElectronic/EMF_Meters/10_LED_EMF_Meter_Replica/r2/doc/10_LED_EMF_Meter_r2_1.pdf

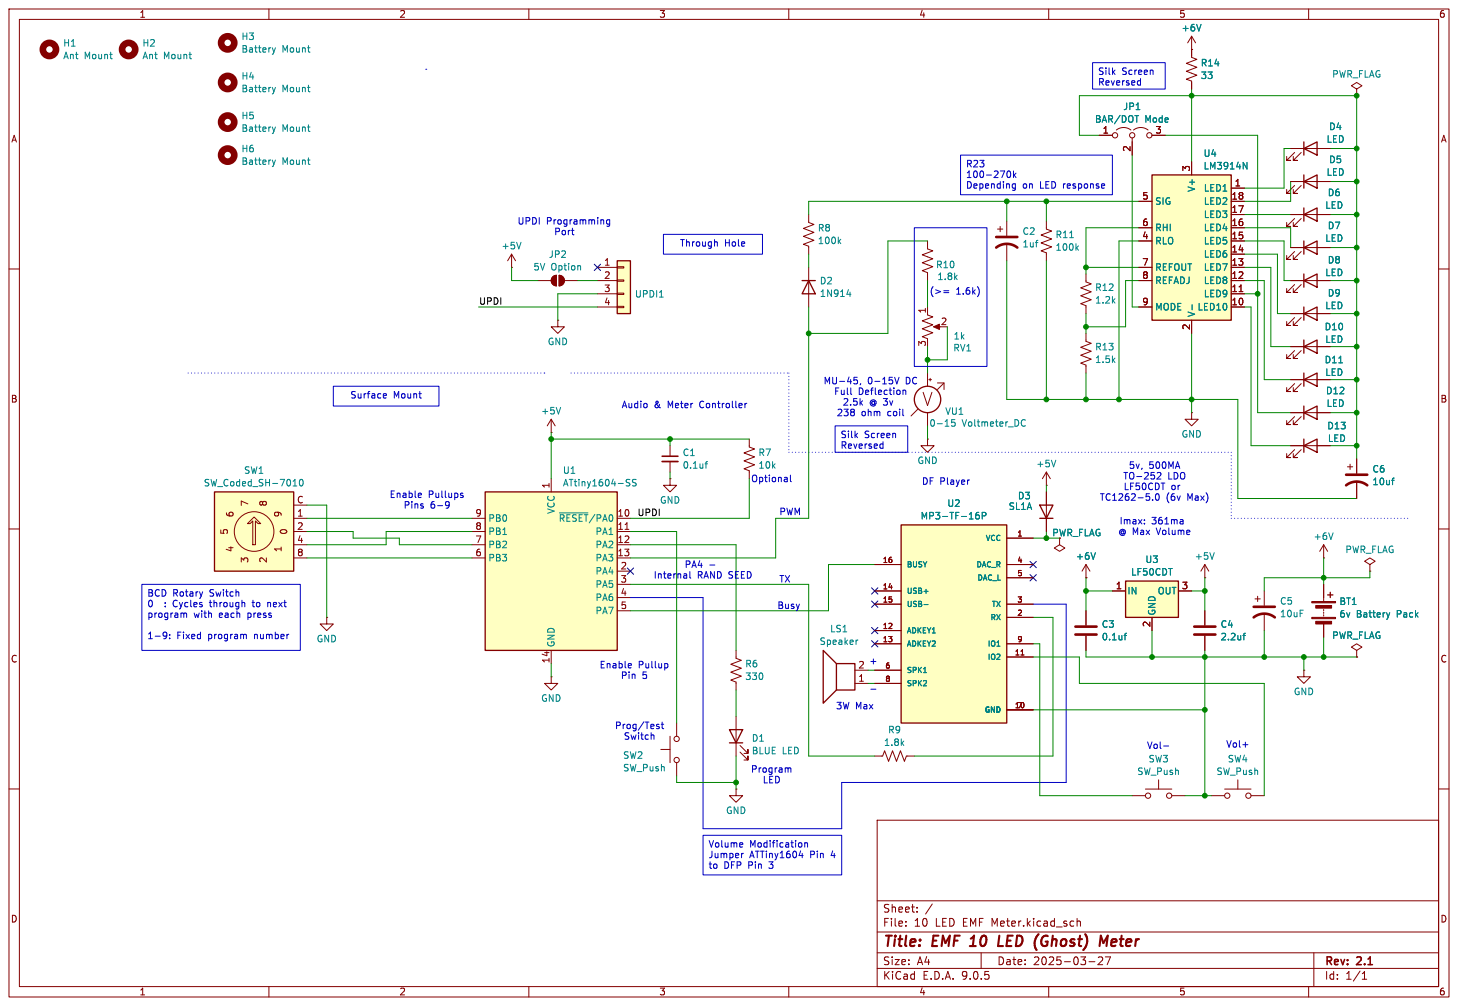
[picture p169: page 1]

UPDI Programming Port Enable Pullups Pins 6-9
~{RESET}/PA010 PA1 11 PA2 12 PA3 13 PA4 2 PA5 3 PA6 4 PA7 5 U1ATtiny1604-SS GND

to DFP Pin 3Busy TX

Imax: 361ma @ Max Volume DF Player 3W Max Optional PWM
