JohnnyElectronic/EMF_Meters/EMF_Meter_Replica/r1/schematics/EMF_Meter.pdf

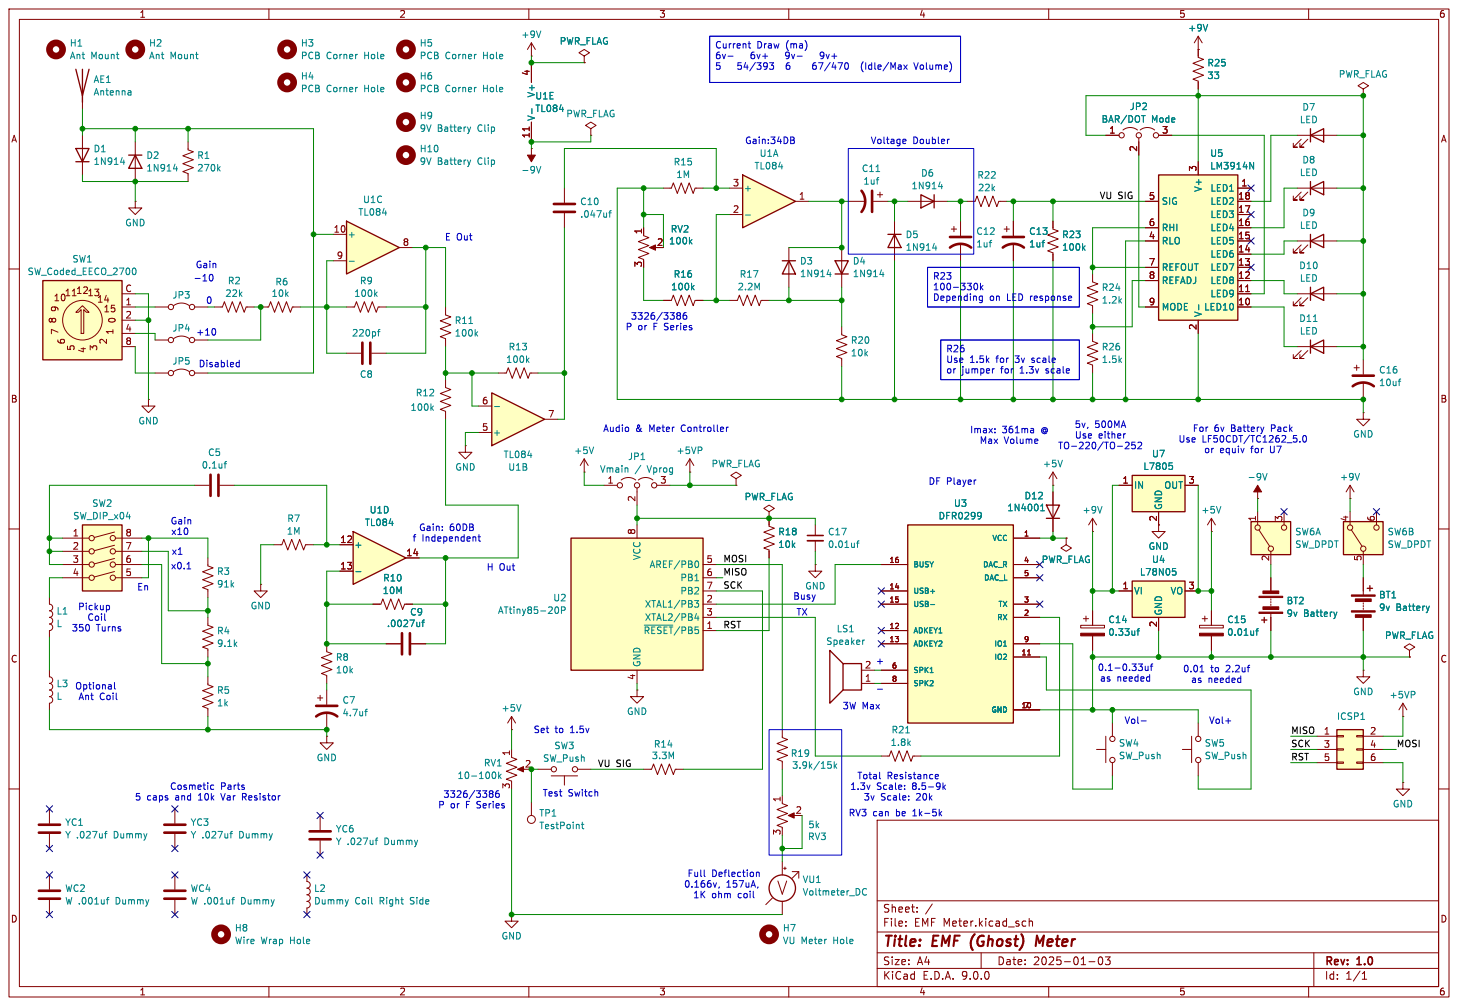
[picture p170: page 1]

or equiv for U7 RV3 can be 1k-5k TX R10

0.01 to 2.2uf as needed Vol- Full Deflection
